OakTreeWC/12KEMPV2.1/Photos/IMG_2421.jpg

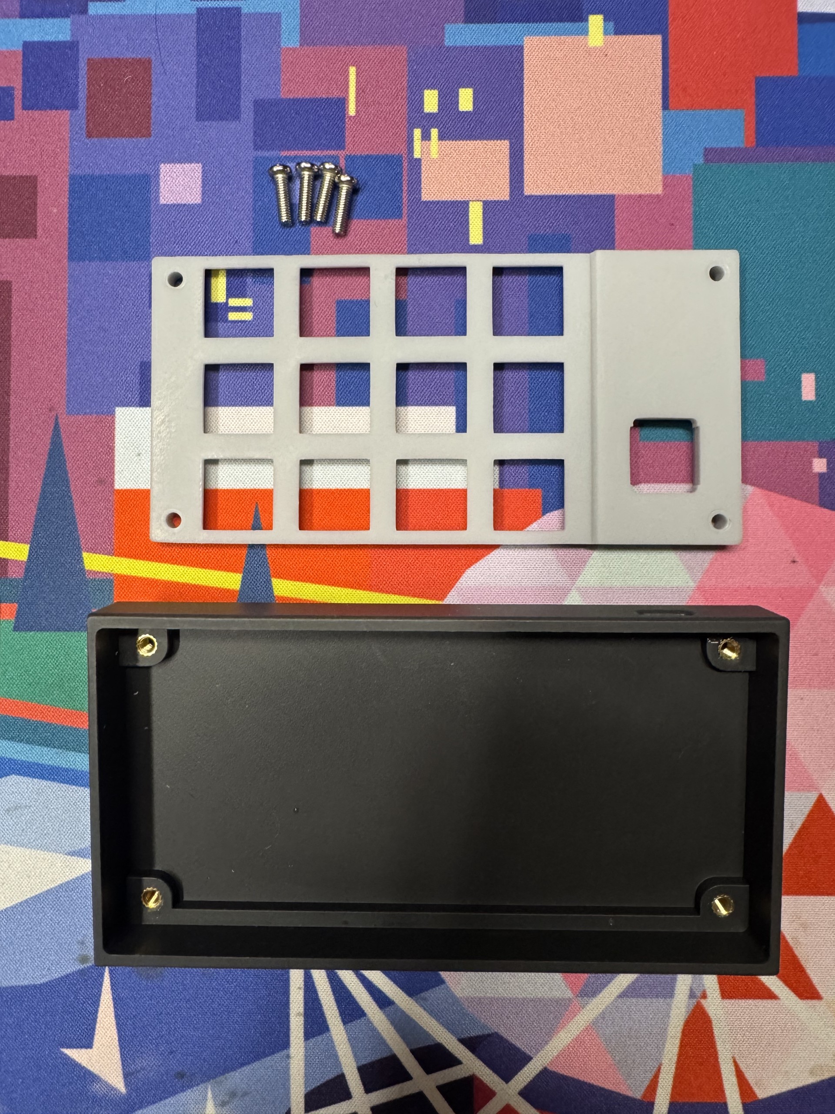
Photos/IMG_2421.jpg
