OakTreeWC/12KEMPV2.1/Photos/IMG_2422.jpg

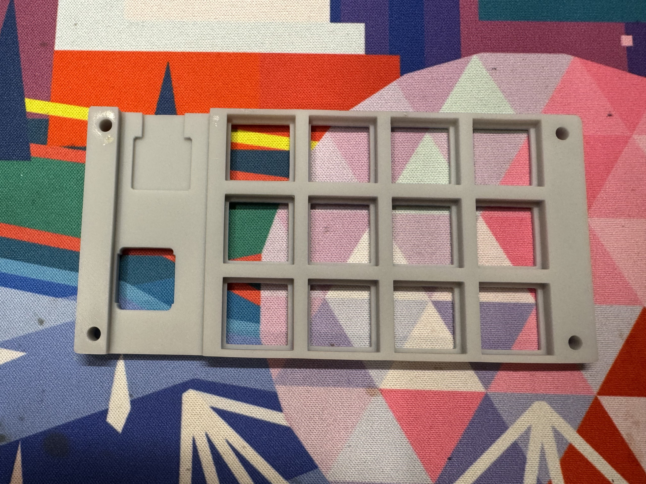
Photos/IMG_2422.jpg
