OakTreeWC/12KEMPV2.1/Photos/IMG_2425.jpg

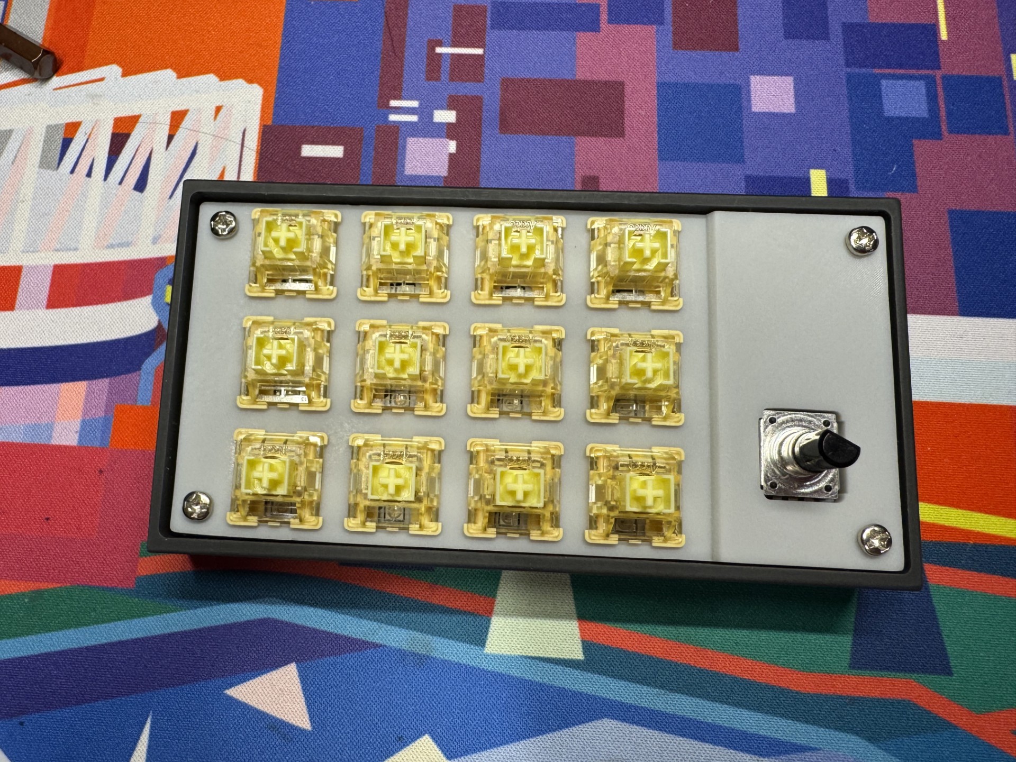
Photos/IMG_2425.jpg
