OakTreeWC/12KEMPV2.1/Photos/IMG_2426.jpg

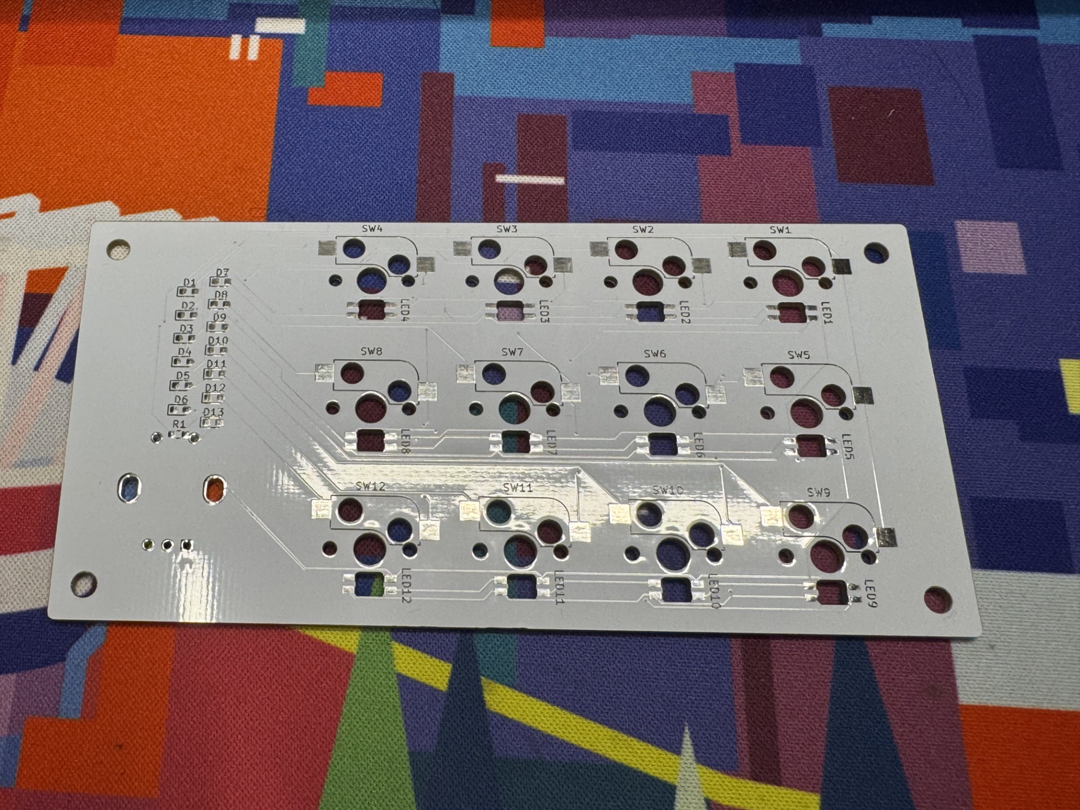
Photos/IMG_2426.jpg
