OakTreeWC/12KEMPV2.1/Photos/IMG_2427.jpg

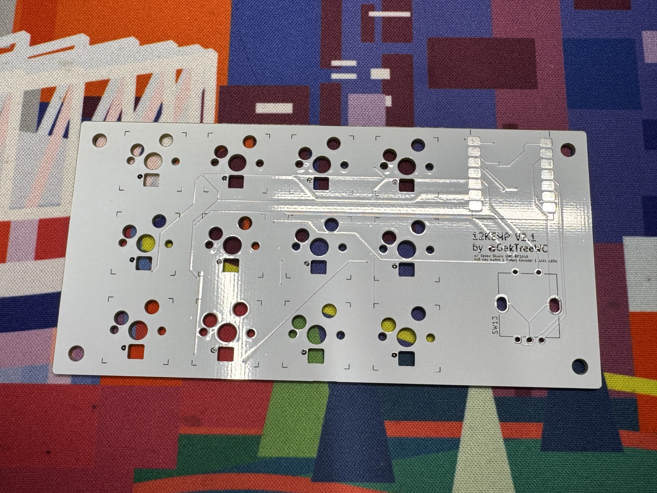
Photos/IMG_2427.jpg
