OakTreeWC/12KEMPV2.1/Photos/IMG_2428.jpg

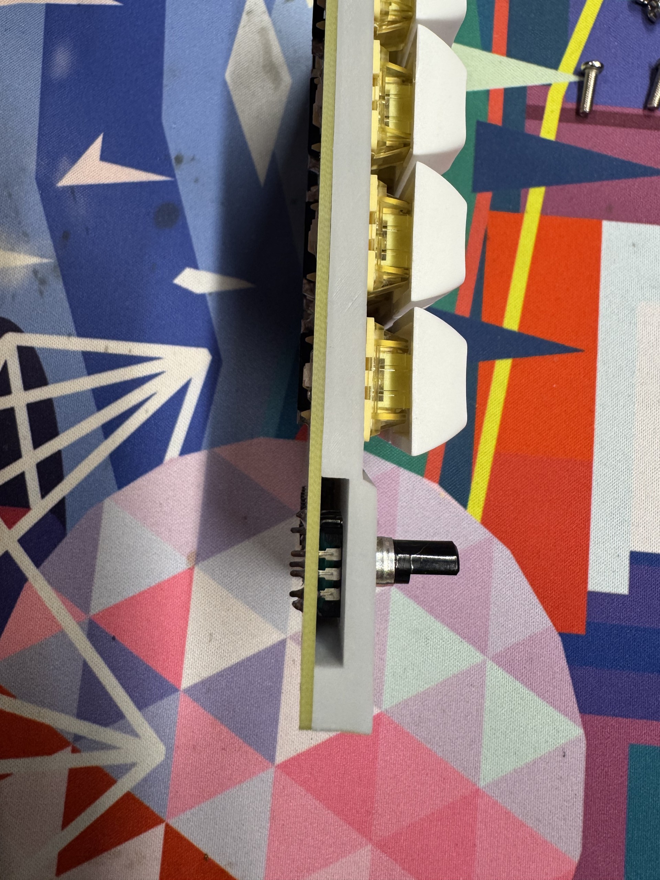
Photos/IMG_2428.jpg
