OakTreeWC/12KEMPV2.1/Photos/IMG_2429.jpg

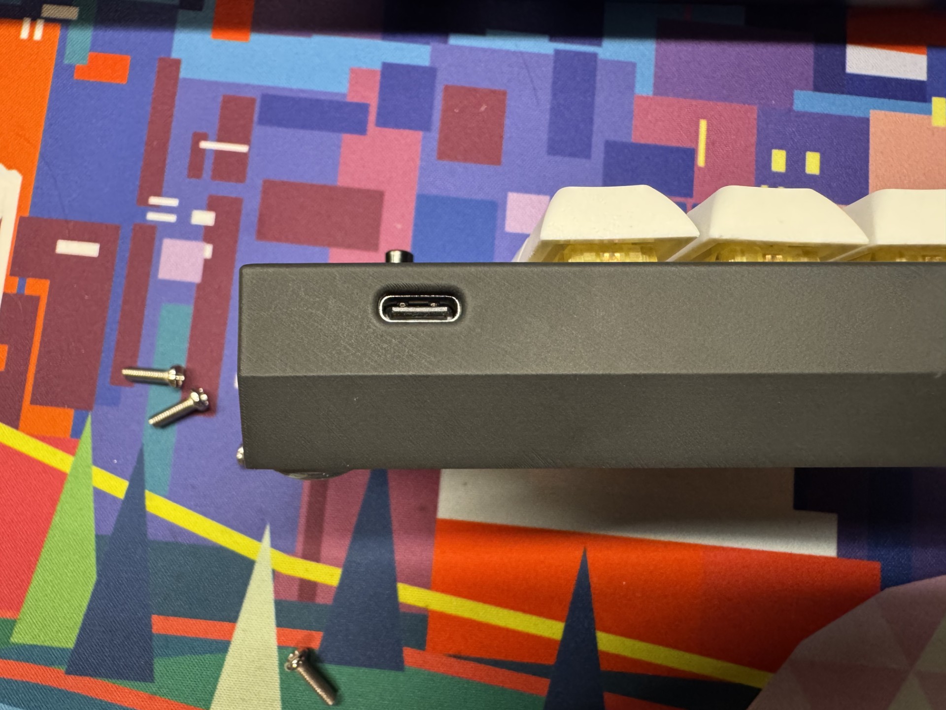
Photos/IMG_2429.jpg
