OakTreeWC/12KEMPV2.1/Photos/IMG_E2430.jpg

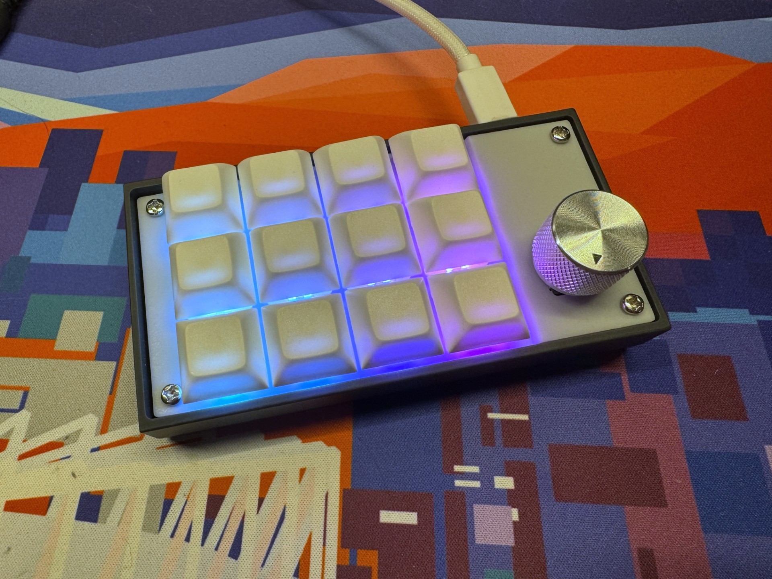
Photos/IMG_E2430.jpg
